hceTnaF/ForInfo/4.docs/2-1.png

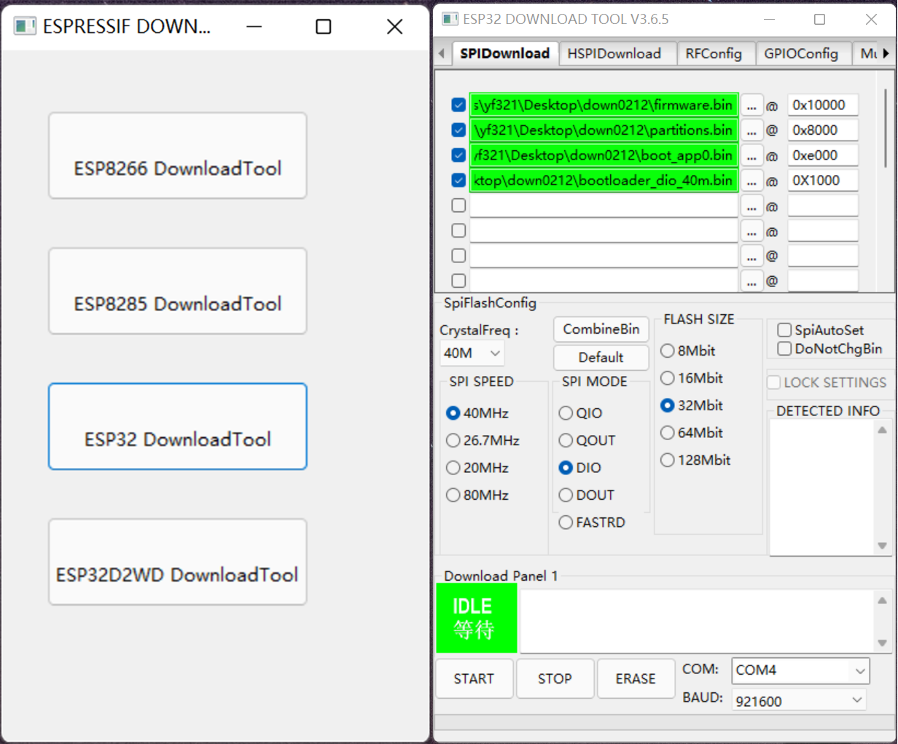
4.docs/2-1.png
