hceTnaF/ForInfo/4.docs/ForInfo_1.png

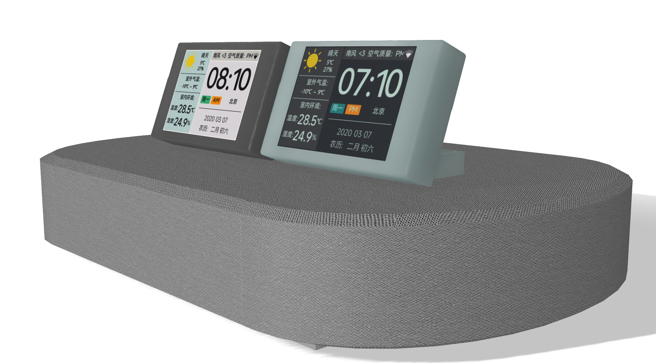
4.docs/ForInfo_1.png
